diego-card/codCentrifuge/todosOsTestesCentrifuga/Balanceados/4-amostras-2agua-2vazio.csv

Time | X-axis | Y-axis | Z-axis | Temperature
00:00:00 | 133.0 | 120.0 | 3.0 | 24.0
00:00:02 | 135.0 | 121.0 | 3.0 | 24.0
00:00:03 | 136.0 | 121.0 | 3.0 | 24.0
00:00:03 | 132.0 | 122.0 | 3.0 | 24.0
00:00:03 | 133.0 | 122.0 | 5.0 | 24.0
00:00:03 | 133.0 | 121.0 | 3.0 | 24.0
00:00:03 | 134.0 | 119.0 | 3.0 | 24.0
00:00:04 | 135.0 | 120.0 | 4.0 | 24.0
00:00:04 | 136.0 | 121.0 | 2.0 | 24.0
00:00:04 | 134.0 | 120.0 | 3.0 | 24.0
00:00:04 | 131.0 | 120.0 | 5.0 | 24.0
00:00:04 | 134.0 | 120.0 | 4.0 | 24.0
00:00:05 | 133.0 | 119.0 | 4.0 | 24.0
00:00:05 | 134.0 | 120.0 | 4.0 | 24.0
00:00:05 | 134.0 | 120.0 | 2.0 | 24.0
00:00:05 | 136.0 | 120.0 | 0.0 | 24.0
00:00:05 | 135.0 | 121.0 | 4.0 | 24.0
00:00:06 | 135.0 | 120.0 | 4.0 | 24.0
00:00:06 | 133.0 | 120.0 | 3.0 | 24.0
00:00:06 | 134.0 | 119.0 | 4.0 | 24.0
00:00:06 | 135.0 | 120.0 | 4.0 | 24.0
00:00:06 | 134.0 | 121.0 | 4.0 | 24.0
00:00:07 | 135.0 | 120.0 | 4.0 | 24.0
00:00:07 | 134.0 | 121.0 | 4.0 | 24.0
00:00:07 | 137.0 | 118.0 | 2.0 | 24.0
00:00:07 | 132.0 | 123.0 | 5.0 | 24.0
00:00:07 | 139.0 | 119.0 | 2.0 | 24.0
00:00:08 | 135.0 | 123.0 | 0.0 | 24.0
00:00:08 | 134.0 | 121.0 | 3.0 | 24.0
00:00:08 | 133.0 | 119.0 | 4.0 | 24.0
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
