diego-card/codCentrifuge/todosOsTestesCentrifuga/Balanceados/4-amostras-com-agua-mesmo-volume.csv

Time | X-axis | Y-axis | Z-axis | Temperature
00:00:00 | 132.0 | 120.0 | 5.0 | 27.0
00:00:02 | 134.0 | 120.0 | 5.0 | 27.0
00:00:03 | 132.0 | 121.0 | 4.0 | 27.0
00:00:03 | 128.0 | 121.0 | 7.0 | 27.0
00:00:03 | 135.0 | 118.0 | 4.0 | 27.0
00:00:03 | 132.0 | 122.0 | 4.0 | 27.0
00:00:03 | 132.0 | 120.0 | 5.0 | 27.0
00:00:04 | 133.0 | 118.0 | 5.0 | 27.0
00:00:04 | 134.0 | 119.0 | 4.0 | 27.0
00:00:04 | 136.0 | 119.0 | 5.0 | 27.0
00:00:04 | 133.0 | 120.0 | 6.0 | 27.0
00:00:04 | 133.0 | 118.0 | 5.0 | 27.0
00:00:04 | 134.0 | 119.0 | 4.0 | 27.0
00:00:05 | 133.0 | 118.0 | 7.0 | 27.0
00:00:05 | 132.0 | 120.0 | 5.0 | 27.0
00:00:05 | 132.0 | 119.0 | 5.0 | 27.0
00:00:05 | 133.0 | 121.0 | 6.0 | 27.0
00:00:06 | 136.0 | 120.0 | 4.0 | 27.0
00:00:06 | 133.0 | 120.0 | 5.0 | 27.0
00:00:06 | 131.0 | 119.0 | 6.0 | 27.0
00:00:06 | 132.0 | 119.0 | 3.0 | 27.0
00:00:06 | 132.0 | 119.0 | 6.0 | 27.0
00:00:07 | 133.0 | 119.0 | 5.0 | 27.0
00:00:07 | 133.0 | 119.0 | 4.0 | 27.0
00:00:07 | 132.0 | 118.0 | 5.0 | 27.0
00:00:07 | 132.0 | 119.0 | 3.0 | 27.0
00:00:07 | 132.0 | 119.0 | 5.0 | 27.0
00:00:08 | 134.0 | 120.0 | 5.0 | 27.0
00:00:08 | 134.0 | 121.0 | 5.0 | 27.0
00:00:08 | 134.0 | 121.0 | 5.0 | 27.0
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
