diego-card/codCentrifuge/todosOsTestesCentrifuga/Balanceados/4-amostras-vazias.csv

Time | X-axis | Y-axis | Z-axis | Temperature
00:00:00 | 133.0 | 120.0 | 4.0 | 26.0
00:00:02 | 131.0 | 122.0 | 3.0 | 26.0
00:00:03 | 131.0 | 120.0 | 4.0 | 26.0
00:00:03 | 133.0 | 122.0 | 5.0 | 26.0
00:00:03 | 131.0 | 123.0 | 4.0 | 26.0
00:00:03 | 132.0 | 122.0 | 4.0 | 26.0
00:00:03 | 130.0 | 118.0 | 4.0 | 26.0
00:00:04 | 131.0 | 121.0 | 6.0 | 26.0
00:00:04 | 135.0 | 119.0 | 4.0 | 26.0
00:00:04 | 130.0 | 118.0 | 4.0 | 26.0
00:00:04 | 133.0 | 120.0 | 2.0 | 26.0
00:00:04 | 132.0 | 117.0 | 4.0 | 26.0
00:00:04 | 133.0 | 118.0 | 3.0 | 26.0
00:00:05 | 133.0 | 119.0 | 5.0 | 26.0
00:00:05 | 133.0 | 119.0 | 2.0 | 26.0
00:00:05 | 133.0 | 119.0 | 4.0 | 26.0
00:00:05 | 132.0 | 118.0 | 3.0 | 26.0
00:00:06 | 132.0 | 119.0 | 4.0 | 26.0
00:00:06 | 137.0 | 119.0 | 4.0 | 26.0
00:00:06 | 133.0 | 117.0 | 6.0 | 26.0
00:00:06 | 133.0 | 118.0 | 3.0 | 26.0
00:00:06 | 134.0 | 120.0 | 3.0 | 26.0
00:00:07 | 130.0 | 117.0 | 5.0 | 26.0
00:00:07 | 130.0 | 123.0 | 3.0 | 26.0
00:00:07 | 136.0 | 124.0 | 2.0 | 26.0
00:00:07 | 134.0 | 124.0 | 3.0 | 26.0
00:00:07 | 133.0 | 119.0 | 3.0 | 26.0
00:00:08 | 133.0 | 119.0 | 3.0 | 26.0
00:00:08 | 134.0 | 120.0 | 3.0 | 26.0
00:00:08 | 137.0 | 123.0 | 0.0 | 26.0
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
